Circuit-Digest/BLE-Dice/Documents & Images/BLE Dice SoC IMU.png

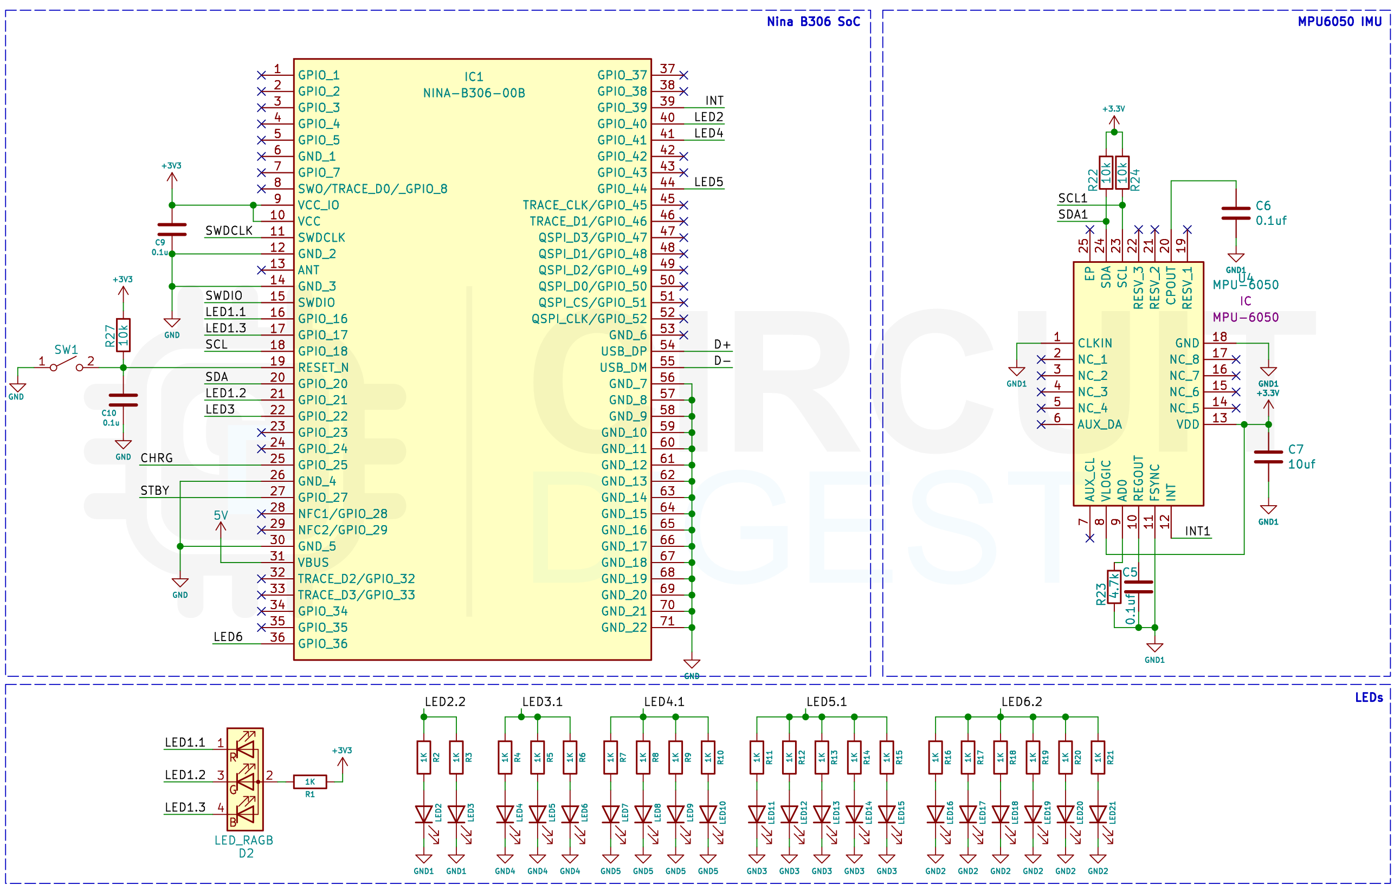
Documents & Images/BLE Dice SoC IMU.png
