Circuit-Digest/BLE-Dice/Documents & Images/DiceBottom3D.png

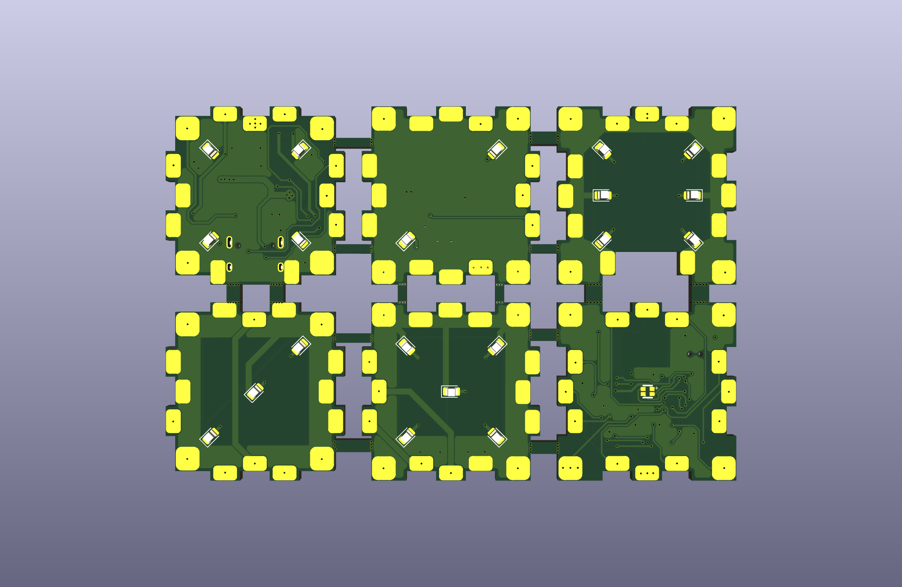
Documents & Images/DiceBottom3D.png
