Circuit-Digest/BLE-Dice/Documents & Images/PCB_BOTTOM.png

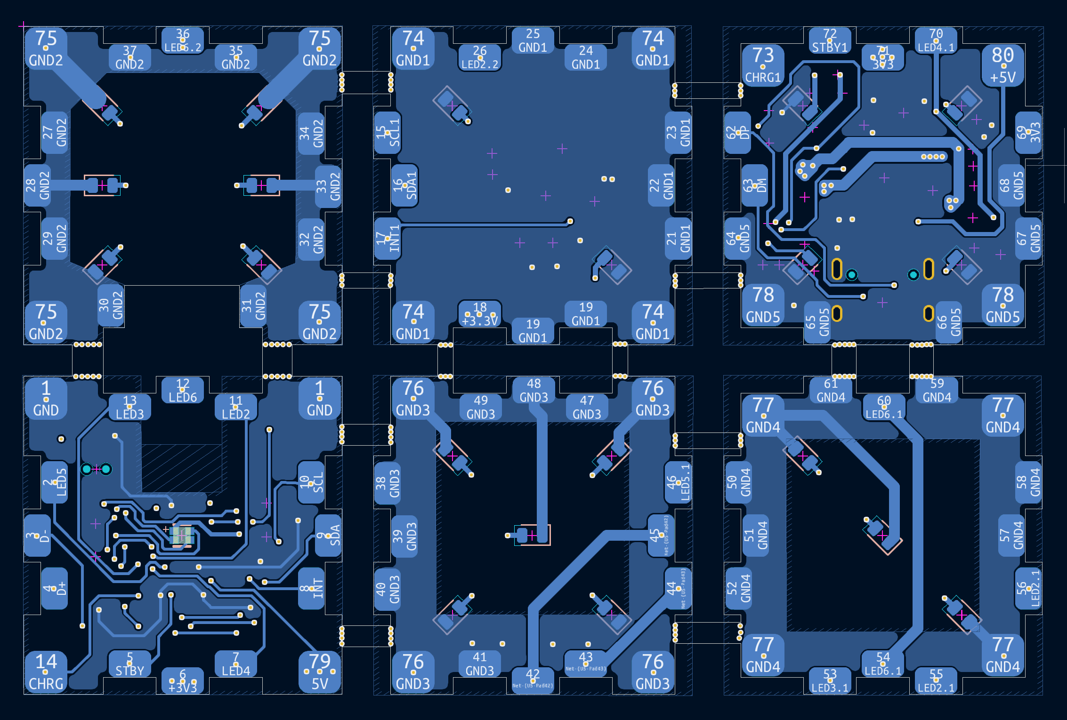
Documents & Images/PCB_BOTTOM.png
