Circuit-Digest/BLE-Dice/Documents & Images/PCB_TOP.png

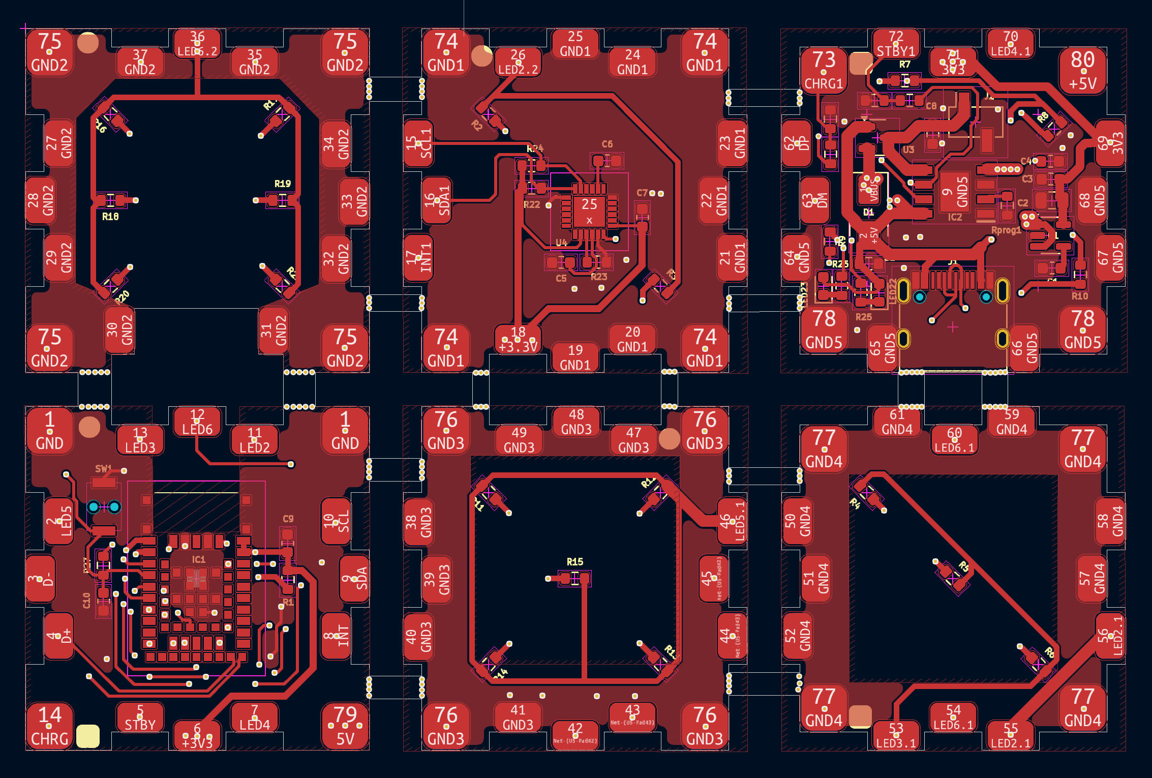
Documents & Images/PCB_TOP.png
